esar/vivepos/solve-lighthouse.py

#!/usr/bin/python

"""
   Copyright (C) 2018 Stephen Robinson
  
   This file is part of vivepos
  
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
"""


import os
import sys
import time
import math
import argparse
import serial
import struct
import binascii
import collections
import numpy as np
import scipy.optimize

TICK_CLOCK_MHZ = 5.0
SWEEP_CENTER_IN_MICROSEC = 4000
SWEEP_180_IN_MICROSEC = 8333


def ticks2angle(ticks):
	return math.pi * (ticks / TICK_CLOCK_MHZ - SWEEP_CENTER_IN_MICROSEC) / SWEEP_180_IN_MICROSEC


def angles2vector(xAngle, yAngle):
	plane1 = np.double([+math.cos(xAngle), 0, -math.sin(xAngle)])
	plane2 = np.double([0, +math.cos(yAngle), +math.sin(yAngle)])
	vector = np.cross(plane2, plane1)
	vector /= np.linalg.norm(vector)
	return vector


def calcRotationMatrix(fromVector, toVector):
	# From http://www.j3d.org/matrix_faq/matrfaq_latest.html#Q38
	# Via https://stackoverflow.com/questions/43507491/imprecision-with-rotation-matrix-to-align-a-vector-to-an-axis

	# Normalize vector length
	toVector /= np.linalg.norm(toVector)
	fromVector /= np.linalg.norm(fromVector)

	# Get axis
	uvw = np.cross(fromVector, toVector)

	# compute trig values - no need to go through arccos and back
	rcos = np.dot(fromVector, toVector)
	rsin = np.linalg.norm(uvw)

	# normalize and unpack axis
	if not np.isclose(rsin, 0):
		uvw /= rsin
	u, v, w = uvw

	# Compute rotation matrix - re-expressed to show structure
	return (
		rcos * np.eye(3) +
		rsin * np.double([
			[ 0, -w,  v],
			[ w,  0, -u],
			[-v,  u,  0]
		]) +
		(1.0 - rcos) * uvw[:,None] * uvw[None,:]
	)


def calcSensorDistances(sensorGrid, sensorTicks):
	sensorPos = np.array([
		[+sensorGrid/2, -sensorGrid/2, 0],
		[+sensorGrid/2, +sensorGrid/2, 0],
		[-sensorGrid/2, +sensorGrid/2, 0],
		[-sensorGrid/2, -sensorGrid/2, 0]
	])

	# Calc distances between sensors
	r01 = np.linalg.norm(sensorPos[0] - sensorPos[1])
	r02 = np.linalg.norm(sensorPos[0] - sensorPos[2])
	r03 = np.linalg.norm(sensorPos[0] - sensorPos[3])
	r12 = np.linalg.norm(sensorPos[1] - sensorPos[2])
	r13 = np.linalg.norm(sensorPos[1] - sensorPos[3])
	r23 = np.linalg.norm(sensorPos[2] - sensorPos[3])

	v0 = angles2vector(ticks2angle(sensorTicks[0][0]), ticks2angle(sensorTicks[0][1]))
	v1 = angles2vector(ticks2angle(sensorTicks[1][0]), ticks2angle(sensorTicks[1][1]))
	v2 = angles2vector(ticks2angle(sensorTicks[2][0]), ticks2angle(sensorTicks[2][1]))
	v3 = angles2vector(ticks2angle(sensorTicks[3][0]), ticks2angle(sensorTicks[3][1]))

	v01 = np.dot(v0, v1)
	v02 = np.dot(v0, v2)
	v03 = np.dot(v0, v3)
	v12 = np.dot(v1, v2)
	v13 = np.dot(v1, v3)
	v23 = np.dot(v2, v3)

	funcs = [
		# See https://trmm.net/Lighthouse for derivation of equations
		lambda k0,k1,k2,k3: k0**2 + k1**2 - 2*k0*k1*v01 - r01**2,
		lambda k0,k1,k2,k3: k0**2 + k2**2 - 2*k0*k2*v02 - r02**2,
		lambda k0,k1,k2,k3: k0**2 + k3**2 - 2*k0*k3*v03 - r03**2,
		lambda k0,k1,k2,k3: k2**2 + k1**2 - 2*k2*k1*v12 - r12**2,
		lambda k0,k1,k2,k3: k3**2 + k1**2 - 2*k3*k1*v13 - r13**2,
		lambda k0,k1,k2,k3: k2**2 + k3**2 - 2*k2*k3*v23 - r23**2,

		# Prefer solutions where the lengths differ by less than the grid size
		lambda k0,k1,k2,k3: max(sensorGrid, abs(k0-k1))-sensorGrid + 
		                    max(sensorGrid, abs(k0-k2))-sensorGrid + 
		                    max(sensorGrid, abs(k0-k3))-sensorGrid + 
		                    max(sensorGrid, abs(k1-k2))-sensorGrid + 
		                    max(sensorGrid, abs(k1-k3))-sensorGrid + 
		                    max(sensorGrid, abs(k2-k3))-sensorGrid
	]
	func = lambda x: [f(*x) for f in funcs]
	solution = scipy.optimize.leastsq(func, [1000, 1000, 1000, 1000])
	solution = solution[0]

	#print "solution: ", solution

	points = [
		np.double(v0 * solution[0]),
		np.double(v1 * solution[1]),
		np.double(v2 * solution[2]),
		np.double(v3 * solution[3])
	]

	errors = {
		'01': np.linalg.norm(points[0] - points[1]) - r01,
		'02': np.linalg.norm(points[0] - points[2]) - r02,
		'03': np.linalg.norm(points[0] - points[3]) - r03,
		'12': np.linalg.norm(points[1] - points[2]) - r12,
		'13': np.linalg.norm(points[1] - points[3]) - r13,
		'23': np.linalg.norm(points[2] - points[3]) - r23
	}

	return (points, errors)


def solve(sensorGrid, sensorTicks):
	sensorPoints, errors = calcSensorDistances(sensorGrid, sensorTicks)

	# Calculate the normal vector of each corner of the sensor plane
	# as seen by the lighthouse
	planeNormals = [
		np.cross(sensorPoints[1] - sensorPoints[0], sensorPoints[0] - sensorPoints[3]),
		np.cross(sensorPoints[0] - sensorPoints[1], sensorPoints[2] - sensorPoints[1]),
		np.cross(sensorPoints[1] - sensorPoints[2], sensorPoints[3] - sensorPoints[2]),
		np.cross(sensorPoints[2] - sensorPoints[3], sensorPoints[0] - sensorPoints[3])
	]

	# Average the normals and convert to unit vector
	averageNormal = np.double([0, 0, 0])
	for normal in planeNormals:
		averageNormal += normal
	averageNormal /= len(planeNormals)
	averageNormal /= np.linalg.norm(averageNormal)

	# Calculate rotation from plane normal as seen by lighthouse
	# to plane normal from the sensor's point of view
	rotationMatrixToFlat = calcRotationMatrix(averageNormal, np.double([0, 1, 0]))
	
	# Calculate center of plane as seen by lighthouse
	center1 = sensorPoints[0] + ((sensorPoints[2] - sensorPoints[0]) / 2)
	center2 = sensorPoints[1] + ((sensorPoints[3] - sensorPoints[1]) / 2)
	averageCenter = (center1 + center2) / 2

	# Translate lighthouse and sensor points so that they are centered on the origin
	# and rotate so they are flat (Z is stright up from the sensor plane)
	lighthousePoint = rotationMatrixToFlat.dot(-averageCenter)
	sensorPoints[0] = rotationMatrixToFlat.dot(sensorPoints[0] - averageCenter)
	sensorPoints[1] = rotationMatrixToFlat.dot(sensorPoints[1] - averageCenter)
	sensorPoints[2] = rotationMatrixToFlat.dot(sensorPoints[2] - averageCenter)
	sensorPoints[3] = rotationMatrixToFlat.dot(sensorPoints[3] - averageCenter)

	# Calculate the rotation around the sensor normal vector
	# to get X and Y in the correct orientation and rotate the points into place
	rotationMatrix = calcRotationMatrix(sensorPoints[1] - sensorPoints[0], np.double([1, 0, 0]))
	lighthousePoint = rotationMatrix.dot(lighthousePoint)
	sensorPoints[0] = rotationMatrix.dot(sensorPoints[0])
	sensorPoints[1] = rotationMatrix.dot(sensorPoints[1])
	sensorPoints[2] = rotationMatrix.dot(sensorPoints[2])
	sensorPoints[3] = rotationMatrix.dot(sensorPoints[3])

	# Calculate the rotation matrix to convert from lighthouse to world	
	lighthouseRotationMatrix = rotationMatrix.dot(rotationMatrixToFlat)

	return {
		'rotation': lighthouseRotationMatrix, 
		'origin': lighthousePoint, 
		'sensorPoints': sensorPoints, 
		'errors': errors
	}


def rotateForGravity(solution1, solution2, ootx1, ootx2):
	v1 = np.double([ootx1['accel_dir_x'], ootx1['accel_dir_y'], ootx1['accel_dir_z']])
	v1 /= np.linalg.norm(v1)
	v1 = solution1['rotation'].dot(v1)

	v2 = np.double([ootx2['accel_dir_x'], ootx2['accel_dir_y'], ootx2['accel_dir_z']])
	v2 /= np.linalg.norm(v2)
	v2 = solution2['rotation'].dot(v2)

	vAverage = (v1 + v1) / 2
	rotationMatrix = calcRotationMatrix(vAverage, np.double([0, 0, -1]))

	solution1['rotation'] = rotationMatrix.dot(solution1['rotation'])
	solution1['origin'] = rotationMatrix.dot(solution1['origin'])
	for i in range(len(solution1['sensorPoints'])):
		solution1['sensorPoints'][i] = rotationMatrix.dot(solution1['sensorPoints'][i])

	solution2['rotation'] = rotationMatrix.dot(solution2['rotation'])
	solution2['origin'] = rotationMatrix.dot(solution2['origin'])
	for i in range(len(solution2['sensorPoints'])):
		solution2['sensorPoints'][i] = rotationMatrix.dot(solution2['sensorPoints'][i])


def intersectLines(origin1, ray1, origin2, ray2):
	w0 = origin1 - origin2
	a = ray1[0]*ray1[0] + ray1[1]*ray1[1] + ray1[2]*ray1[2]
	b = ray1[0]*ray2[0] + ray1[1]*ray2[1] + ray1[2]*ray2[2]
	c = ray2[0]*ray2[0] + ray2[1]*ray2[1] + ray2[2]*ray2[2]
	d = ray1[0]*w0[0] + ray1[1]*w0[1] + ray1[2]*w0[2]
	e = ray2[0]*w0[0] + ray2[1]*w0[1] + ray2[2]*w0[2]

	denom = a*c - b*b

	if denom > -0.00001 and denom < 0.00001:
		return (False, 0, 0)

	t = (b * e - c * d) / denom
	p1 = ray1 * t
	p1 += origin1

	t = (a * e - b * d) / denom
	p2 = ray2 * t
	p2 += origin2

	result = (p1 + p2) / 2
	distance = np.linalg.norm(p1 - p2)
	
	return (True, result, distance)


def verify(sensorGrid, ticks1, ticks2, lighthouse1, lighthouse2):
	sensorPos = np.array([
		[+sensorGrid/2, -sensorGrid/2, 0],
		[+sensorGrid/2, +sensorGrid/2, 0],
		[-sensorGrid/2, +sensorGrid/2, 0],
		[-sensorGrid/2, -sensorGrid/2, 0]
	])

	for i in range(len(ticks1)):
		ray1 = angles2vector(ticks2angle(ticks1[i][0]), ticks2angle(ticks1[i][1]))
		ray2 = angles2vector(ticks2angle(ticks2[i][0]), ticks2angle(ticks2[i][1]))

		ray1 = lighthouse1['rotation'].dot(ray1)
		ray2 = lighthouse2['rotation'].dot(ray2)

		success, result, distance = intersectLines(
			lighthouse1['origin'], ray1,
			lighthouse2['origin'], ray2
		)

		if success:
			print "sensor %u:" % i
			print "\tintersect distance: ", distance
			print "\tlocation: ", result
			print "\terror:    ", result - sensorPos[i]
		else:
			print "sensor %u: error, rays are parallel" % i


def decodeOotx(data):
	data = data[0:33*2]
	Record = collections.namedtuple('v6', 
		'fw_version id fcal_0_phase fcal_1_phase fcal_0_tilt fcal_1_tilt ' +
		'sys_unlock_count hw_version fcal_0_curve fcal_1_curve accel_dir_x ' +
		'accel_dir_y accel_dir_z fcal_0_gibphase fcal_1_gibphase fcal_0_gibmag ' +
		'fcal_1_gibmag mode_current sys_faults'
	)
	return Record._asdict(Record._make(struct.unpack('<HIhhhhBBhhbbbhhhhBB', binascii.unhexlify(data))))


def dumpAngle(line):
	if not hasattr(dumpAngle, 'cnt'):
		dumpAngle.cnt = 0
		dumpAngle.min = [1000000, 1000000, 1000000, 1000000]
		dumpAngle.max = [-1000000, -1000000, -1000000, -1000000]
		dumpAngle.avg = [0, 0, 0, 0]
	if line == None:
		if hasattr(dumpAngle, 'cnt'):
			print "\ntotal: ", dumpAngle.cnt
			labels = ['0X', '0Y', '1X', '1Y']
			for i in range(4):
				print labels[i] + ':'
				print "\trange: ", abs(dumpAngle.max[i] - dumpAngle.min[i])
				print "\tmin: ", dumpAngle.min[i]
				print "\tmax: ", dumpAngle.max[i]
				print "\tavg: ", dumpAngle.avg[i]/dumpAngle.cnt
		return

	data = line.split(',', 4)
	if len(data) == 5:
		for i in range(4):
			val = float(data[i+1])
			if val < dumpAngle.min[i]: dumpAngle.min[i] = val
			if val > dumpAngle.max[i]: dumpAngle.max[i] = val
			dumpAngle.avg[i] += val
		dumpAngle.cnt += 1
		print "%s:    %5s:%5s    %5s:%5s" % tuple(data)

def dumpPosition(line):
	if not hasattr(dumpPosition, 'cnt'):
		dumpPosition.cnt = 0
		dumpPosition.min = [1000000, 1000000, 1000000]
		dumpPosition.max = [-1000000, -1000000, -1000000]
		dumpPosition.avg = [0, 0, 0]
	if line == None:
		if hasattr(dumpPosition, 'cnt'):
			print "\ntotal: ", dumpPosition.cnt
			labels = ['X', 'Y', 'Z']
			for i in range(3):
				print labels[i] + ':'
				print "\trange: ", abs(dumpPosition.max[i] - dumpPosition.min[i])
				print "\tmin: ", dumpPosition.min[i]
				print "\tmax: ", dumpPosition.max[i]
				print "\tavg: ", dumpPosition.avg[i]/dumpPosition.cnt
		return

	data = line.split(',', 4)
	if len(data) == 5:
		for i in range(3):
			val = float(data[i+1])
			if val < dumpPosition.min[i]: dumpPosition.min[i] = val
			if val > dumpPosition.max[i]: dumpPosition.max[i] = val
			dumpPosition.avg[i] += val
		dumpPosition.cnt += 1
		print "%s:    X: %8s    Y: %8s    Z: %8s    err: %s" % tuple(data)

def dumpOotx(line):
	if line == None:
		return

	data = line.split(',')
	if len(data) == 3:
		r = decodeOotx(data[2])
		print "Lighthouse %s:" % data[0]
		for name, value in r.iteritems():
			print "\t%s: %s" % (name, value)

def dumpLighthouse(line):
	if line == None:
		return

	data = line.split(',')
	if len(data) == 13:
		print "Lighthouse %s:" % data[0]
		print "\tOrigin: %s %s %s" % (data[1], data[2], data[3])
		print "\tRotation:"
		print "\t\t%s %s %s" % (data[4], data[5], data[6])
		print "\t\t%s %s %s" % (data[7], data[8], data[9])
		print "\t\t%s %s %s" % (data[10], data[11], data[12])


def dumpLighthouseError(line):
	if line == None:
		return

	data = line.split(',')
	if len(data) == 6:
		print "Solution Error:"
		print "\tErr01: ", data[0]
		print "\tErr02: ", data[1]
		print "\tErr03: ", data[2]
		print "\tErr12: ", data[3]
		print "\tErr13: ", data[4]
		print "\tErr23: ", data[5]


def dumpStatus(line):
	if line == None:
		return

	print line


def dumpData(input, sensor, count, angles, ootx, position, lighthouse, status):
	try:
		while True:
			line = input.readline()
			if not line: break
			line = line.strip()

			if sensor != None:
				try:
					if (not line.startswith('S:')) and (not line.startswith('E:')) and int(line[2:].split(',')[0]) != sensor:
						continue
				except ValueError:
					# ignore
					print "value error"

			if count != None:
				if count == 0:
					break

			matches = 0
			if line.startswith('A:') and angles:
				matches += 1
				dumpAngle(line[2:])
			elif line.startswith('P:') and position:
				matches += 1
				dumpPosition(line[2:])
			elif line.startswith('D:') and ootx:
				matches += 1
				dumpOotx(line[2:])
			elif line.startswith('L:') and lighthouse:
				matches += 1
				dumpLighthouse(line[2:])
			elif line.startswith('E:') and lighthouse:
				matches += 1
				dumpLighthouseError(line[2:])
			elif line.startswith('S:') and status:
				matches += 1
				dumpStatus(line[2:])

			if count != None:
				count -= matches
	except KeyboardInterrupt:
		# do nothing
		angles = angles

	if angles: dumpAngle(None)
	if position: dumpPosition(None)
	if ootx: dumpOotx(None)


def collectSamples(input, count, collectOOTX=True):
	lighthouse1 = {'ootx':None, 'angles':None}
	lighthouse2 = {'ootx':None, 'angles':None}
	total = 0
	counts = [0, 0, 0, 0]
	lighthouse1Angles = [
		[0, 0],
		[0, 0],
		[0, 0],
		[0, 0]
	]
	lighthouse2Angles = [
		[0, 0],
		[0, 0],
		[0, 0],
		[0, 0]
	]

	n = 0
	while n < count or (collectOOTX and (lighthouse1['ootx'] == None or lighthouse2['ootx'] == None)):
		line = input.readline()

		if line.startswith('D:'):
			data = line[2:-1].split(',')
			if len(data) == 3:
				lh = int(data[0])
				if lh == 0 and lighthouse1['ootx'] == None:
					sys.stderr.write('O1')
					lighthouse1['ootx'] = decodeOotx(data[2])
				elif lh == 1 and lighthouse2['ootx'] == None:
					sys.stderr.write('O2')
					lighthouse2['ootx'] = decodeOotx(data[2])
			
		if not line.startswith('A:') or n >= count:
			sys.stderr.write('.')
			continue
		line = line[2:-1]

		cols = line.split(',', 6)
		i = int(cols[0])
		if i < 0 or i > len(lighthouse1Angles):
			sys.stderr.write('X')
			continue

		total += 1
		counts[i] += 1
		lighthouse1Angles[i][0] += int(cols[1])
		lighthouse1Angles[i][1] += int(cols[2])
		lighthouse2Angles[i][0] += int(cols[3])
		lighthouse2Angles[i][1] += int(cols[4])

		sys.stderr.write('*')
		n += 1

	sys.stdout.write('\n')

	for i in range(4):
		lighthouse1Angles[i][0] /= counts[i]
		lighthouse1Angles[i][1] /= counts[i]
		lighthouse2Angles[i][0] /= counts[i]
		lighthouse2Angles[i][1] /= counts[i]

	lighthouse1['angles'] = lighthouse1Angles
	lighthouse2['angles'] = lighthouse2Angles

	return (lighthouse1, lighthouse2)


def printSolutionText(solutions):
	for index, solution in enumerate(solutions):
		print "lighthouse %u:" % index
		print "\trotation: "
		for row in solution['rotation']:
			print "\t\t", row
		print "\tposition: "
		print "\t\t", solution['origin']
		print "\terrors: "
		for name, value in solution['errors'].iteritems():
			print "\t\t%s: %.04fmm" % (name, value)
		print


def printSolutionC(solutions):
	print "static lighthouse_t g_lighthouses[%u] =" % len(solutions)
	print "{"
	for i, solution in enumerate(solutions):
		print "\t{"
		print "\t\t{"
		for j, row in enumerate(solution['rotation']):
			if j != len(solution['rotation']) - 1:
				c = ','
			else:
				c = ''
			print "\t\t\t%.05f, %.05f, %.05f%s" % (row[0], row[1], row[2], c)
		print "\t\t},"
		print "\t\t{"
		print "\t\t\t%.05f, %.05f, %.05f" % (
			solution['origin'][0], 
			solution['origin'][1], 
			solution['origin'][2]
		)
		print "\t\t}"
		if i == len(solutions) - 1:
			print "\t}"
		else:
			print "\t},"
	print "};"


def printSolutionGnuplot(solutions):
	for solution in solutions:
		lr = solution['rotation']
		lp = solution['origin']
		sp = solution['sensorPoints']
		err = solution['errors']

		v = lambda v: ' '.join([str(x) for x in v])

		# draw lighthouse normal
		print v(lp), v(lr.dot([0, 0, 100])), 0

		# draw vectors from lighthouse to sensors
		print v(lp), v(sp[0] - lp), 0
		print v(lp), v(sp[1] - lp), 1
		print v(lp), v(sp[2] - lp), 2
		print v(lp), v(sp[3] - lp), 3

		# draw sensor plane
		print v(sp[0]), v(sp[1] - sp[0]), 0
		print v(sp[0]), v(sp[2] - sp[0]), 0
		print v(sp[0]), v(sp[3] - sp[0]), 0
		print v(sp[1]), v(sp[2] - sp[1]), 1
		print v(sp[1]), v(sp[3] - sp[1]), 1
		print v(sp[2]), v(sp[3] - sp[2]), 2

	sys.stderr.write('plot with: splot "FILENAME" using 1:2:3:4:5:6:7 with vectors lc palette\n')



parser = argparse.ArgumentParser()
parser.add_argument('input', type=str,
	help='input source: filename, serial device (e.g. /dev/ttyS0), or "-" for stdin')
parser.add_argument('--format', type=str,
	help='output format: text (default), c, gnuplot',
	default='text')
parser.add_argument('--bps', type=int,
	help='BPS for serial input (default 115200)',
	default=115200)
parser.add_argument('--count', type=int,
	help='number of samples to collect and average (default 50)',
	default=50)
parser.add_argument('--grid', type=int,
	help='sensor grid spacing in mm (default 30)',
	default=30)
parser.add_argument('--no-gravity', action='store_true',
	help='don\'t rotate the solution so that down matches lighthouse accelerometers',
	default=False)
parser.add_argument('--verify', action='store_true',
	help='verify result by triangulating sensor positions',
	default=False)
parser.add_argument('--dump-angles', action='store_true',
	help='write angle data to stdout, don\'t calc solution',
	default=False)
parser.add_argument('--dump-ootx', action='store_true',
	help='write OOTX data to stdout, don\'t calc solution',
	default=False)
parser.add_argument('--dump-pos', action='store_true',
	help='write position data to stdout, don\'t calc solution',
	default=False)
parser.add_argument('--dump-lighthouse', action='store_true',
	help='write lighthouse position/rotation to stdout, don\'t calc solution',
	default=False)
parser.add_argument('--dump-status', action='store_true',
	help='write status messages to stdout, don\'t calc solution',
	default=False)
parser.add_argument('--dump-sensor', type=int,
	help='restrict dump output to a single sensor',
	default=None)
parser.add_argument('--dump-count', type=int,
	help='restrict the number of items dumped',
        default=None)
args = parser.parse_args()

input = None
if args.input == '-':
	input = sys.stdin
elif os.path.isfile(args.input):
	input = open(args.input)
elif os.path.exists(args.input):
	input = serial.Serial(args.input, args.bps)
	time.sleep(0.1)
	input.flushInput()
	input.readline() # discard first, probably partial, line
else:
	print "can't open %s" % args.input
	sys.exit(1)

if args.dump_angles or args.dump_ootx or args.dump_pos or args.dump_lighthouse or args.dump_status:
	dumpData(input, args.dump_sensor, args.dump_count, args.dump_angles, args.dump_ootx, args.dump_pos, args.dump_lighthouse, args.dump_status)
	sys.exit(1)

lighthouse1, lighthouse2 = collectSamples(input, args.count, not args.no_gravity)
solution1 = solve(args.grid, lighthouse1['angles'])
solution2 = solve(args.grid, lighthouse2['angles'])
if not args.no_gravity:
	rotateForGravity(solution1, solution2, lighthouse1['ootx'], lighthouse2['ootx'])

if args.format == 'text':
	printSolutionText((solution1, solution2))
elif args.format == 'c':
	printSolutionC((solution1, solution2))
elif args.format == 'gnuplot':
	printSolutionGnuplot((solution1, solution2))
else:
	print 'unknown output format'

if args.verify:
	verify(args.grid, lighthouse1['angles'], lighthouse2['angles'], solution1, solution2)
