esar/vivepos/lighthouse_pos.h

static lighthouse_t g_lighthouses[2] =
{
	{
		{
			-0.16846, 0.02080, -0.98549,
			0.98494, -0.03604, -0.16913,
			-0.03904, -0.99913, -0.01441
		},
		{
			-583.82751, -111.91662, -523.92959
		}
	},
	{
		{
			0.69376, -0.14305, 0.70585,
			-0.20243, -0.97930, 0.00050,
			0.69117, -0.14323, -0.70836
		},
		{
			748.00879, -65.28995, -882.45659
		}
	}
};
